flucas96/ESP12_Button/button_timer v1.2.1_Coin_Cell[TPL5110] - corrected/V1.2.1 Coin Cell [Maße].jpg

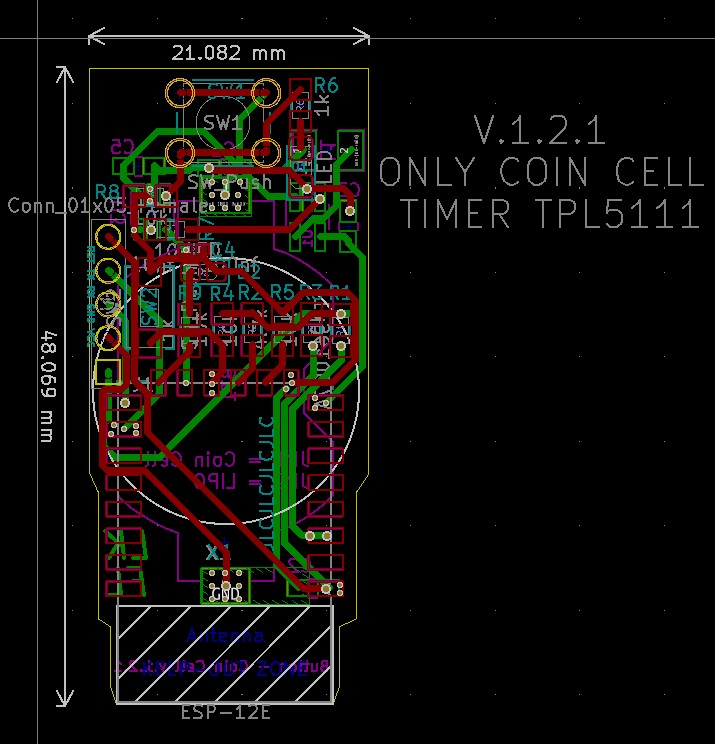
button_timer v1.2.1_Coin_Cell[TPL5110] - corrected/V1.2.1 Coin Cell [Maße].jpg
